EngThi/nablaCalc/hardware/procurement/evidence/aliexpress_display_2.2in_no_touch_usd_6.22.png

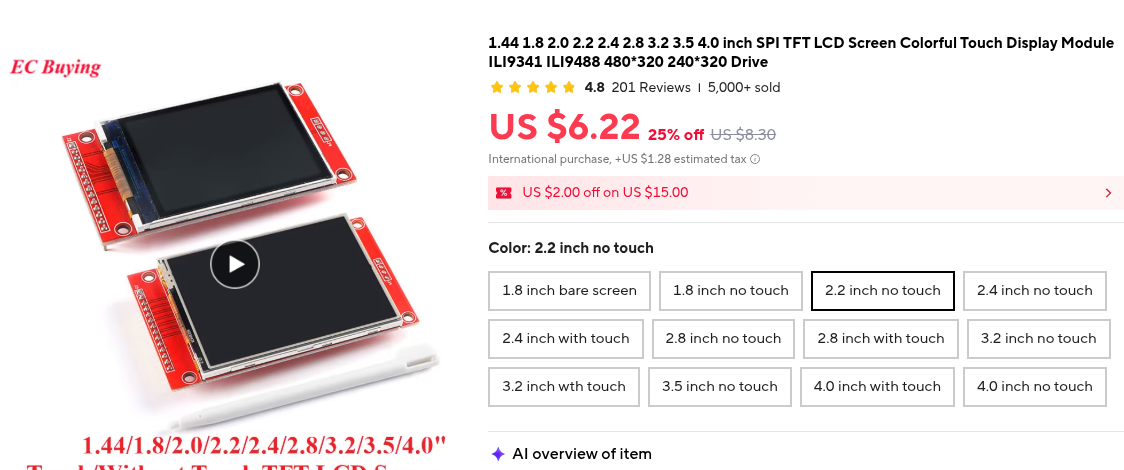
hardware/procurement/evidence/aliexpress_display_2.2in_no_touch_usd_6.22.png
