EngThi/nablaCalc/hardware/procurement/evidence/jlcone_top_pcba_quote_usd_86.18.png

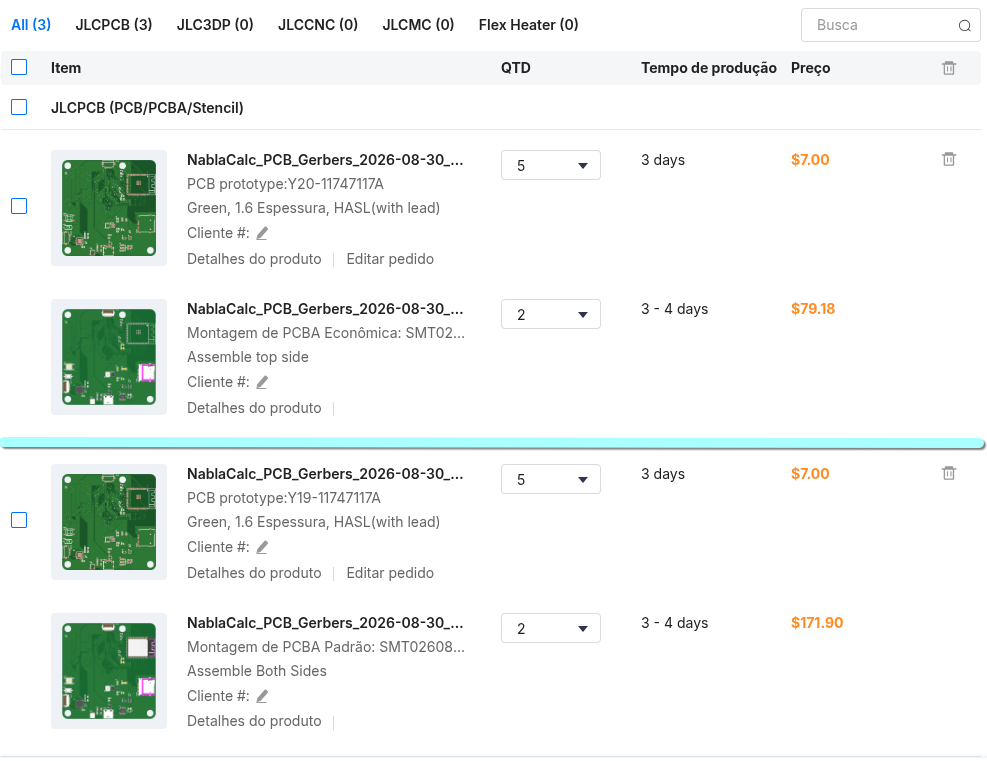
hardware/procurement/evidence/jlcone_top_pcba_quote_usd_86.18.png
