EngThi/nablaCalc/hardware/procurement/evidence/mercadolivre_battery_503450_brl_37.89.png

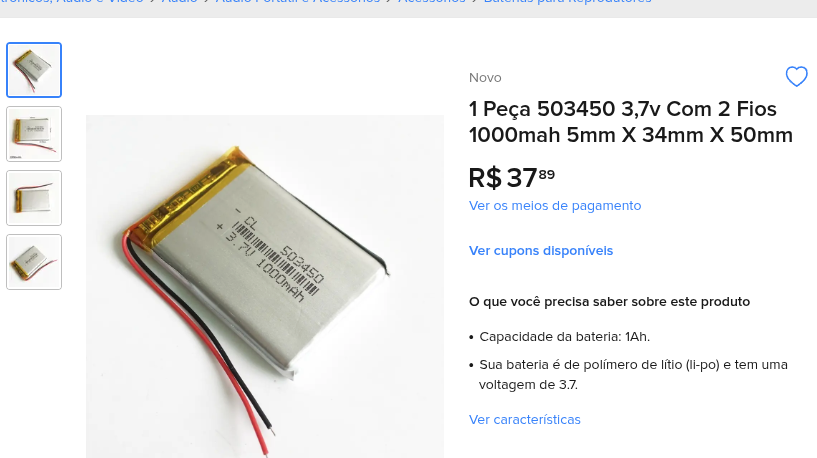
hardware/procurement/evidence/mercadolivre_battery_503450_brl_37.89.png
